RamboRogers/deadmansinternet/image-6.png

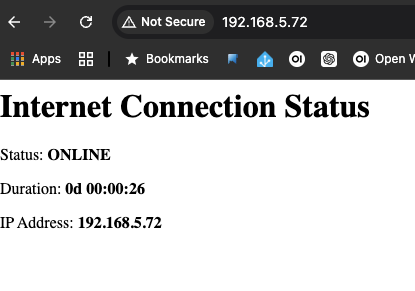
image-6.png
